christopherwang0129SE/monkey-office/3d Model officemonkey.dk/chat-notes/2026-05-23-sessions.md

# Chat-noter — 2026-05-23

> **Note:** Disse er historiske chat-noter. Fil-referencer nedenfor matcher den oprindelige flade struktur fra 2026-05-23. Repo'et blev omstruktureret samme aften — se [`../README.md`](../README.md) for nuværende lokationer (`product/`, `design/`, `hardware/`).

Noter fra chat-session om visuel design af noise-monkey produktet.

## Spørgsmål fra Gustav

> "Kan du se planning for the office monkey hvordan den skal være? Skal vi prøve at lave et billede af den med nano banana for at backward-engineere?"

## Hvad findes (kortlagt i chatten)

Planning ligger i `agent360-jesperai/agent360/docs/planning/`:

- `2026-05-23-product-plan.md` — koncept låst: 3D-printet desk-abe, hænder-over-mund når dB-tærskel brydes, solgt per-desk/per-zone + dB-dashboard
- `2026-05-23-noise-monkey-research.md` — business outcome research (66% produktivitetstab, 86 min/dag, 23 min refokus, etc.)
- `2026-05-23-noise-monkey-killer-usps-deck.md` — USP-deck
- `2026-05-23-noise-monkey-sales-strategy.md` — sales-strategi
- `2026-05-23-competitor-research-and-usp.md` — konkurrent-research

I dette repo (`office-monkey-hackaton`) på chat-tidspunktet (før restrukturering):
- `Mokey-product-plan.md`, `Research.md`, `PRINT.md`, `design-v1.md`, `design-critique.md`
- `cad/`, `stl/`, `prints/`

(Disse filer ligger nu i `hardware/dev-brief.md`, `product/research.md`, `hardware/PRINT.md`, `design/brief.md`, `design/critique.md`.)

## Gap

**Visuel / industriel design-spec eksisterer ikke endnu.** Fase 1 "Product design" i `product-plan.md:21` er stadig uafkrydset. Vi har funktionel beskrivelse, men ingen "sådan skal den se ud"-dokument.

## Beslutning

Brug **nano banana** (Google Gemini 2.5 Flash Image i AI Studio) til at backward-engineere den visuelle identitet:
generer billede først → afled 3D-printbar spec, kulturel-fit-beslutning (åbent spørgsmål i `product-plan.md:54`), og cold-call collateral derfra. Billigere end design-loops.

## Starter-prompt til nano banana

```
A small 3D-printed desk figurine of a stylized monkey, sitting on a modern
office desk next to a laptop and coffee cup. The monkey is in a clear
"hands-over-mouth" pose — both palms pressed firmly over its mouth, eyes
wide, slightly embarrassed expression. Matte finish, single-color resin
(warm off-white), roughly 8-10cm tall. Clean low-poly aesthetic suitable
for a Scandinavian office (think Hay / Muuto desk accessories — not toy,
not childish). A subtle dB-sensor microphone-grille on the chest, almost
hidden. Soft daylight from a window, shallow depth of field, product-shot
style. No text, no logos.
```

## Foreslåede næste skridt

1. Skriv 3-4 prompt-varianter (Scandi / japansk kawaii / brutalist / plush-toy) til A/B i nano banana
2. Lav design-spec doc (`2026-05-23-noise-monkey-design-spec.md`) som placeholder der udfyldes når valgt billede er låst
3. Afklar åbne spørgsmål i `product-plan.md:50-54` — særligt kulturel fit af "hænder-over-mund" gesten (DE/FR/US/JP)

## Status

Ingen kode ændret. Ingen filer skrevet udover denne note. Næste handling = generer billeder med nano banana.

---

# Chat-noter — 2026-05-23 (session 2: business research, USP, sales strategy)

Anden chat-session samme dag. Fokus: forretnings-research, USP-formulering, og sales-strategi for noise-monkey produktet.

## Hvad denne session producerede (4 docs, nu i dette repo)

1. **`2026-05-23-product-plan.md`** — Fase 1/2 skelet med låst produkt-definition (3D-printet desk-abe, dækker munden ved dB-tærskel).
2. **`2026-05-23-noise-monkey-research.md`** — 13-sektion dyb business outcome research med ~25 kilder. Fem hovedtal:
   - 66 % produktivitetstab ved én overhørt samtale (Banbury & Berry 2005)
   - 86 min/dag tabt i åbent kontor (Steelcase × IPSOS, 10 500 medarbejdere)
   - 23 min 15 s refokus efter afbrydelse (Gloria Mark, UC Irvine)
   - 35 % tilfredse med kontor-støj (Leesman 2024-25)
   - Distraktion = 93,6 % af årligt produktivitetstab — 15× mere end sygefravær
3. **`2026-05-23-noise-monkey-killer-usps-deck.md`** — 9-slide præsentations-pakke med 5 rangerede USP'er:
   - 🥇 "Shush'en ingen tager personligt" (moaten)
   - 🥈 ROI-tabel: €26-325k/år tabt afhængig af team-størrelse
   - 🥉 ESG-rapport-bevis (WELL v2 + ISO 45003)
   - Zoom-kald-kvalitet
   - Kontorets talisman
4. **`2026-05-23-noise-monkey-sales-strategy.md`** — 12-ugers 0-til-30-betalende-kunder plan. Demo-først strategi: aben sælger sig selv på et bord i 60 sek. Kanaler rangeret (walk-in > cold-call > LinkedIn > Product Hunt). 3-tier pricing (€99/€499/€999) med 30-dages risk-free pilot som universal close.

## Centrale beslutninger der venter (denne uge)

- [ ] Target-segment for uge 3-6 (anbefalet: KBH tech/scale-up 50-200 ansatte)
- [ ] Hardware-leverandør: selv-print vs. Sculpteo/Shapeways for første 30 units
- [ ] Pris-anchor i pitch: €99 vs. €499 (anbefalet: €499 office pack — under godkendelses-grænse)
- [ ] Landing-page placering: agent360.dk/aben vs. separat domæne
- [ ] Benjamins rolle — cold-call ejerskab eller Gustav solo

## Åbne spørgsmål denne session ikke løste

- **Verifikation af de fem hovedtal mod primær-kilder** — research er web-summary-baseret. Skal bekræftes inden kunde-decks. **Benjamins research-task (jf. product-plan.md) er ikke landet i nogen repo endnu** — nul commits fra ham per 2026-05-23.
- **Navn til aben** — Hush Monkey / Quiet Ape / Shhmpanzee / MonkeyMute. Test mod første 5 kontor-chefer.
- **Kulturel fit af "hænder-over-mund" gesten** i DE/FR/US/JP — overlap med session-1 spørgsmål (visuel design).
- **Hardware BOM** — vi gætter €15-35/unit; ikke verificeret med prototype endnu.

## Hvor vi ER (status ved session-slut)

- ✅ Forretnings-research, USP, sales-strategi: dokumenteret
- ❌ Prototype: nul aber bygget
- ❌ Kunde: nul betalende, nul piloter
- ❌ Landing-page: eksisterer ikke
- ❌ Benjamin: nul input

Det er **dag 0** af 12-ugers planen. Næste konkrete valg:
- **A)** Byg hardware (5 aber, 7 dage) → walk-in mandag uge 2
- **B)** Valider købsvilje med 20 cold-calls FØR vi bygger hardware (anbefalet — sparer €500-1500 hvis pitch er forkert)

## Status

Alle 4 docs committet i `agent360-jesperai/agent360/docs/planning/` (commits 944dc9fb9 → a65d17f52, branch `new-website-branch`). Nu også kopieret til dette repo på `gustav-chat-noter` branch.
