christopherwang0129SE/monkey-office/three-wise-monkeys-website-inspiration.md

# Website Inspiration from the Three Wise Monkeys Story

This concept works best as a symbolic, atmospheric website built around perception, restraint, and moral choice rather than a literal or playful monkey theme. The central proverb is commonly expressed as “see no evil, hear no evil, speak no evil,” and is associated with the three figures Mizaru, Kikazaru, and Iwazaru. Sources also connect the motif to Japanese visual culture, especially the well-known carving at the Tōshōgū Shrine in Nikkō, while noting earlier moral roots linked to Confucian and Buddhist traditions.

## Core Creative Direction

A compelling interpretation is to design the site as a journey through three forms of perception: sight, sound, and speech. Each part of the interface can embody one principle, allowing the story to unfold through transitions, concealment, and controlled revelation rather than direct exposition.

Three strong concept directions emerge from the symbolism:

- **Minimal editorial** — a quiet, refined site with three structured panels or chapters, using typography and white space to suggest contemplation.
- **Immersive symbolic** — a more experimental experience where blur, silence, and redaction gradually resolve into clarity, reflecting moral awareness.
- **Cultural narrative** — a museum-like digital story about the shrine carving, the proverb, and its ethical interpretations across cultures.

## Visual Language

The strongest palette is restrained: bone, charcoal, aged wood, stone, temple red, and one muted teal or moss accent. This aligns with the historical and spiritual framing of the motif better than glossy gradients or bright startup colors.

The art direction can borrow from carved wood, shrine architecture, archival labels, and triptych compositions. A three-part visual system is especially effective because the monkeys are individually tied to seeing, hearing, and speaking, making the number three structurally meaningful rather than decorative.

## Layout Ideas

A homepage can be built around a triptych or three-chamber structure. Instead of presenting three identical feature cards, the design can vary density and scale so each section feels distinct while remaining part of a shared symbolic system.

Suggested structure:

1. **Hero** — a striking line such as “What we refuse shapes what we become,” paired with three abstract marks or masks that respond to cursor movement.
2. **See** — imagery appears partially obscured, then sharpens as the user scrolls, expressing selective vision and moral attention.
3. **Hear** — ambient sound or waveform visuals stay muted until intentionally activated, reinforcing mindful listening.
4. **Speak** — redacted or fragmented text resolves into clear statements, suggesting disciplined speech.
5. **Origins** — an editorial timeline covering the Japanese shrine carving and the broader ethical tradition behind the proverb.
6. **Modern paradox** — a reflective section exploring how the phrase can also imply silence, denial, or complicity when wrongdoing is ignored.

## Interaction Concepts

The site should use interaction as metaphor. Instead of decorative animations, movement should embody withholding, filtering, and disclosure.

Useful motifs include:

- Masked reveals for images and headlines, especially for the “See” section.
- Audio-on-intent interactions rather than autoplay for the “Hear” section.
- Text censorship and restoration effects for the “Speak” section.
- A light/dark mode contrast that shifts the work from reflective spirituality toward moral ambiguity.

## Tone and References

Two interpretive tones are especially strong. The first is philosophical and meditative, presenting the proverb as guidance about ethical discipline. The second is darker and more critical, using the same proverb to explore censorship, avoidance, or the refusal to confront wrongdoing.

Useful moodboard keywords include:

| Direction | Keywords |
|---|---|
| Philosophical | “ethical restraint,” “ritual silence,” “inner discipline” |
| Japanese craft | “wood carving,” “shrine geometry,” “aged lacquer,” “cedar and stone” |
| Editorial | “triptych grid,” “museum label,” “archival minimalism,” “quiet luxury” |
| Critical | “complicity,” “blindness,” “censorship,” “moral ambiguity” |

## Practical Recommendation

The most distinctive version would combine an editorial layout with symbolic interaction. That approach preserves elegance, avoids cliché, and gives the story enough conceptual depth to feel like a designed cultural experience rather than a themed landing page.
