christopherwang0129SE/monkey-office/3d Model officemonkey.dk/product/plan.md

# Product Plan — 2026-05-23

Captured from Gustav's brief on 2026-05-23. This is the raw skeleton; each section below is a placeholder for the actual artifact to be produced. No content has been inferred — only structure.

---

## Product (locked 2026-05-23)

A 3D-printed desk monkey that measures ambient sound (dB) and physically covers its mouth (hands-over-mouth pose) when the noise crosses a configurable threshold. Sold to offices per-desk or per-zone, with an optional dB-logging dashboard for facilities/HR.

## Tasks (artifacts to produce)

- ✅ **Business outcome research facts** — see [research.md](research.md) (research + USP shortlist). Owner: Benjamin to verify primary-source numbers before customer-facing use.
- **Pure product plan** — owner: Gustav

---

## Fase 1 — Plan & sharpen

- [ ] Product planning
- [ ] Product design
- [x] Research USP → turn into a sales weapon — see [killer USPs deck](usps.md)

**Exit criteria for Fase 1:** USP is articulated as a one-line claim a salesperson can lead a cold-call with, and the product spec is concrete enough that build can start in Fase 2 without further design loops.

---

## Fase 2 — Build + go-to-market in parallel

### Product marketing
- [ ] Walk into offices (in-person outreach)
- [ ] Cold call

### Product
- [ ] Put product together
- [ ] 3D printer — put together
- [ ] Add to team — "cold office" hire

**Exit criteria for Fase 2:** A working product is in customers' hands and there is a repeatable outbound motion (office walk-ins + cold calls) generating qualified conversations.

---

## Launch

- [ ] Product Hunt launch — plan the date, asset list, and pre-launch hunter outreach once Fase 2 is delivering

---

## Open questions

- "Add to team — cold office" — is this a hire dedicated to physical office outreach, or someone who works from a cold/cheap office? Clarify role before recruiting.
- LinkedIn outreach was mentioned then dropped — include in Fase 2 marketing, or out of scope?
- Pricing tier to lead with (€99 single / €499-999 office pack / per-seat SaaS)? Decide based on first 10 cold-call signals.
- Cultural / regional fit of the "monkey covers mouth" gesture (DE/FR/US/JP) — confirm before locking figurine.

---

## Status

- Draft v0 — 2026-05-23
- Not yet linked to V0.1 services plan (`v0.1-services-plan.md`) or solo-pivot doc (`2026-05-06-solo-pivot-and-v0.1-services.md`). Decide whether this product is a new V0.1 line item or a separate track.
