christopherwang0129SE/monkey-office/3d Model officemonkey.dk/product/usps.md

# Noise-Monkey — Killer USPs til præsentation

**Formål:** Slide-klare USP'er der gør produktet til en no-brainer for kontor-chef / HR-lead / office manager. Bygget på research i [research.md](research.md).

**Forudsætning:** Køber er ikke teknisk, har wellness-budget, har modtaget støj-klager, og kan godkende €500-1000 uden indkøbsafdeling. Vi sælger ikke et produkt — vi sælger en *beslutning de gerne vil træffe*.

**Pitch-rytme (15 min):** 1 minut "why now" → 5 minutter på USP #1 og #2 (de vinder salget) → 3 minutter på #3-5 (de lukker indvendingerne) → 3 minutter no-brainer-close → 3 minutter Q&A.

---

## SLIDE 1 — Sandheden om dit kontor

> **På et åbent kontor mister hver medarbejder 86 minutter om dagen til støj.**
> Det er ikke en mening. Det er Steelcase × IPSOS på 10 500 medarbejdere.

**Tre tal til slidet:**
- **66 %** produktivitetsfald ved én overhørt samtale i nærheden (Banbury & Berry)
- **23 min 15 s** at fokusere igen efter en afbrydelse (Gloria Mark, UC Irvine)
- **35 %** er tilfredse med støjniveauet på deres kontor (Leesman 2024-25)

**Closing-linje:** *"Du har enten allerede mistet pengene — eller du betaler dem hver dag uden at vide det."*

**Visuel:** En kontor-tegning. Tre rectangles der lyser rødt med tallene. Aben sidder i hjørnet med hænderne for munden, lille og diskret. Ingen logo endnu.

---

## SLIDE 2 — 🥇 USP #1: "Shush'en ingen tager personligt"

> **Aben siger til. Dine medarbejdere gør ikke.**

**Body (slide-tekst):**
Det dyreste problem på et åbent kontor er ikke støjen. Det er at **ingen vil bede en kollega være stille**. Det er socialt giftigt — derfor vokser støjen indtil de produktive medarbejdere arbejder hjemmefra eller siger op.

Aben løser det ved at flytte håndhævelsen væk fra mennesker. Den er datadrevet (dB-grænse), neutral, og endda sjov. Ingen tager det personligt at en abe holder sig for munden.

**Killer-fact:**
> **99 % af medarbejdere siger kontor-støj forringer deres koncentration. 0 % vil sige det til en kollega.** (Steelcase + sund fornuft.)

**Hvorfor denne USP er moaten:**
- Apps måler. → ændrer ikke adfærd.
- Akustik-paneler absorberer. → ændrer ikke adfærd.
- Sound-masking pumper rosa støj ud. → skjuler problemet, ændrer ikke adfærd.
- Lyd-bokse isolerer. → flytter en person ad gangen.
- **Aben er det eneste der ændrer adfærden hos kilden i real-time uden at et menneske skal være "den dårlige fyr".**

**Closing-linje:** *"Du sælger ikke en sensor. Du sælger fred i kontoret."*

**Visuel:** Foto/render af to medarbejdere der griner og dæmper sig selv, mens aben i forgrunden lige har dækket munden. Tekst-overlay: "Den siger til. Du behøver ikke."

---

## SLIDE 3 — 🥈 USP #2: "86 minutter om dagen pr. medarbejder = €1 200-6 500 pr. år"

> **Med 40 ansatte mister du ~€50 000-260 000 om året til støj. Aben koster en brøkdel.**

**ROI-tabel (skal stå på slidet):**

| Medarbejdere | Konservativ recapture (2 %) | Realistisk (5 %) |
| --- | --- | --- |
| 20 | **€26 000/år** | **€65 000/år** |
| 40 | **€52 000/år** | **€130 000/år** |
| 100 | **€130 000/år** | **€325 000/år** |

(Baseret på €69/time loaded cost, 1 880 arbejdstimer/år, jf. Glassdoor + standard 1,3x benefit-multiplier.)

**Killer-fact:**
> **Distraktion var 93,6 % af det årlige produktivitetstab hos én stor amerikansk arbejdsgiver — 15 gange dyrere end sygefravær.** Du har allerede et 7-cifret problem. Du ved bare ikke det.

**Sammenligning (skal vises som søjlediagram):**
- Awair (luftkvalitets-monitor) påstår **$6 500-15 500/medarbejder/år** i produktivitetsgevinst.
- Støj er den **#1 medarbejder-klage** om kontoret. Større end luft.
- Vores påstand er **mere konservativ** end Awairs, og luften har de allerede købt.

**Closing-linje:** *"Hvis aben bare reducerer dit produktivitetstab med 1 %, har den betalt sig hjem i uge 2."*

**Visuel:** Søjlediagram der viser kontorets støj-tab i én stor rød søjle vs. abens pris i en tynd grøn streg. Tilbagebetalings-vinduet markeret i kalender-grafik: "Uge 1 — installation. Uge 2 — break-even. Uge 3+ — ren gevinst."

---

## SLIDE 4 — 🥉 USP #3: "Din ESG-rapport lover wellbeing. Hvor er dB-loggen?"

> **Du kan ikke rapportere på en metric du ikke måler. Vi giver dig metric'en og audit-trail'en.**

**Body:**
WELL Building Standard v2 kræver max NC 40 i åbne kontorer, NC 35 i lukkede. **ISO 45003 (2021)** — den globale standard for psykisk arbejdsmiljø — definerer **støj som en anerkendt psykosocial fare**. Tilsynsmyndigheder i UK, EU og Nordamerika skifter fra at tjekke politikker til at kræve **dokumentation af systematisk håndtering**.

Dit ESG-bilag og din arbejdsmiljø-rapport siger "vi beskytter medarbejdernes trivsel". Aben er det eneste produkt på markedet der **leverer beviset løbende**.

**Killer-fact:**
> **Når en arbejdsmiljø-tilsyn spørger hvordan I håndterer psykisk arbejdsmiljø, har du så data — eller har du en mening?**

**Hvem dette overbeviser:**
- HR / People & Culture (de skal levere ESG-S tallene)
- Legal (de vil have audit-trail)
- CSR / Sustainability lead (de mangler S-pillar-metrics)
- Bestyrelses-medlem der har ESG på agendaen

**Closing-linje:** *"Det her er ikke en gadget. Det er en compliance-artefakt der ligner en abe."*

**Visuel:** Dashboard-screenshot der viser dB-graf over tid, med thresholds markeret. Side om side med uddrag af WELL v2 / ISO 45003-tekst der nævner støj. Tekst-overlay: "Politik → bevis."

---

## SLIDE 5 — USP #4: "Bedre Zoom-opkald uden at flytte en væg"

> **Hver eneste call leaker dit kontor til kunder. Microsoft og Zoom byggede AI for at fjerne støjen i skyen. Vi fjerner den ved kilden.**

**Body:**
I 2026 er kontoret en **lyd-arena**. Møder er kamera-på, mikrofon-på, hele dagen. Microsoft Teams har shippet **tre niveauer af AI-baseret støj-reduktion** specifikt fordi den underliggende støj er universel — og det fortæller dig at problemet er for stort til at fixe i skyen.

Aben fixer det 1 meter fra mikrofonen, før Teams overhovedet skal arbejde.

**Killer-fact:**
> **Microsoft byggede AI for at skjule din baggrunds-støj. Det er en milliard-dollar tilståelse af at problemet er ufixbart fra cloud'en.**

**Hvem dette overbeviser:**
- Salgs-chefen (reps er i telefonen hele dagen — kunder hører kontoret)
- Customer Success / Support leads (kald-kvalitet = NPS)
- Konsulent-huse, advokat-firmaer, revisorer (klient-fortrolighed)

**Closing-linje:** *"Din næste kunde hører dit kontor før de hører dit pitch. Hvad skal kontoret lyde som?"*

**Visuel:** Split-screen. Venstre: forretningsperson på Zoom med larm bag sig + tekst-overlay "før". Højre: samme person, stille, med aben på bordet bag sig + "efter". Bunden: Microsoft Teams logo + "ships 3-level AI noise suppression — fordi problemet er for stort til kun at løse i softwaren."

---

## SLIDE 6 — USP #5: "Kontorets talisman"

> **Planter, ergo-stole, stå-borde. Alle dine wellness-investeringer er usynlige for kandidater og besøgende. Aben er det første de ser.**

**Body:**
Gen Z og millennials prioriterer trivsel højere end nogen tidligere generation. Glassdoor-anmeldelser nævner ofte "kunne ikke koncentrere mig" og "skulle altid have headphones på" som grund til 1-stjerne.

Aben er **fotografisk, postbar, og signalerer instant** at det her er et sted der tager arbejdsmiljø seriøst. En LinkedIn-post med aben der dækker munden under en travl eftermiddag slår 99 % af employer-brand indhold.

**Killer-fact:**
> **Du har allerede betalt for planter og stå-borde. Ingen ser dem på Glassdoor. Aben er den eneste wellness-investering der er sin egen markedsføring.**

**Hvem dette overbeviser:**
- CHRO / Talent Acquisition
- Founder-CEO i scale-up med kultur-fokus
- Office manager der vil have noget der bliver bemærket
- Marketing-chef der mangler authentic content

**Closing-linje:** *"Hver gang den dækker munden, fortjener I et nyt LinkedIn-billede."*

**Visuel:** En grid af 6 sociale media-stills: aben på et hot-desk, aben med teamet om sig, aben på et investor-besøg, aben i et nyt-ansat-velkomstbillede. Tekst-overlay: "Wellness-investeringer du faktisk kan vise frem."

---

## SLIDE 7 — Hvorfor det her er en no-brainer

**Fire grunde, ét slide:**

### 1. Prisen er under din godkendelses-grænse
Office starter-pack: ~€499-999. Ingen indkøb, ingen approval-chain, ingen forsinkelse. Din wellness-konto kan absorbere det i dag.

### 2. Risk-free trial
Vi sender X aber. Hvis kontoret ikke er mærkbart roligere på 30 dage, betaler du intet. Du har **ingen downside**.

### 3. Det passer i wellness-budgettet du allerede har
Danske firmaer >1000 medarbejdere bruger **$2 400/medarbejder/år** på wellness. Små firmaer ~$720/år. Aben er <1 % af det budget pr. medarbejder — og er den eneste investering du kan måle løbende.

### 4. Du er helten
Det her er **din** beslutning. Aben er synlig. Medarbejdere takker dig. Glassdoor bemærker det. Det er et "did something visible" check i din kvartals-review.

**Closing-linje:** *"Du behøver ikke godkendelse. Du behøver ikke en business case. Du behøver én abe og 30 dage. Hvis du tager fejl, sender du den tilbage."*

---

## SLIDE 8 — Indvendinger & svar

| Indvending | Svar (én linje, læg vægt) |
| --- | --- |
| *"Vi har headphones."* | "Headphones isolerer den der lider. Aben adresserer den der støjer. Du behandler symptom vs. kilde." |
| *"Det er bare en gadget."* | "For medarbejderen er det en gadget. For dig er det et dashboard, et ESG-bilag og en stille office manager-talsmand." |
| *"Det er for dyrt."* | "Det er billigere end at miste én medarbejder. Replacement-cost er 150 % af løn — i jeres tilfælde {beregn}. Aben skal kun forhindre én exit pr. årti for at betale sig hjem." |
| *"Folk vil føle sig overvågede."* | "Den måler dB. Den kender ikke ord. Ingen mikrofon-data forlader enheden. Sammenlign med kameraet i jeres reception." |
| *"Vi har ikke det problem."* | "60 % af kontorer afbrydes af støj mindst 2x/uge. 35 % er tilfredse. Statistisk har I problemet — I har bare normaliseret det." |
| *"Lad os vente til Q4-budget."* | "Hver uge i venter koster jer ~{beregn på 86 min × medarbejdere × €1,15/min} i tabt produktivitet. Beslutningen er ikke om I køber. Den er om I venter med at stoppe blødningen." |
| *"Vi skal lige tale med vores akustiker."* | "Glimrende. Akustik-paneler dæmper alt. Aben targets specifikt den menneskelige støj — adfærd, ikke fysik. De er komplementære, ikke konkurrerende." |

---

## SLIDE 9 — The Close

**Et spørgsmål:**
> "Vil du gerne være den person der løste dette her i denne kvartal — eller den der vidste det og ventede?"

**Et tilbud:**
> "5 aber på dit kontor i 30 dage. Hvis støj-klagerne ikke falder, sender du dem tilbage og betaler nul. Hvis de falder — og det gør de — så fortsætter vi samtalen om rest-licensen."

**Et action-item:**
> "Skal jeg sende dig en pilot-aftale i aften, så I kan starte mandag?"

---

## Bilag — Hvordan denne deck'en bruges

**Til kolde opkald (DKK 30 sek):**
> "Hej, jeg har et produkt der reducerer kontor-støj uden at jeres medarbejdere skal shush'e hinanden. Steelcase siger I taber 86 min/dag/person til støj. Jeg har en abe der løser det. Har du 15 minutter til en demo?"

**Til office-walk-ins:**
- Tag 1-2 aber med
- Stil den på modtagelse-disken under samtalen
- Lad den naturligt dække munden (juster threshold under demo) — dét er pitchen
- Del kontaktet til dig som "den der løser noget vi ikke kan løse selv"

**Til LinkedIn outreach:**
- Headline-hook: USP #1 ("Shush'en ingen tager personligt")
- Body: USP #2 ROI-tabellen
- CTA: USP #7 risk-free-trial

**Til Product Hunt launch:**
- Hero-visuel: aben der dækker munden i et åbent kontor (video, ikke billede)
- Headline: "The noise meter that closes its own mouth"
- Tagline: "Built for the open-plan offices that everyone hates but nobody fixes"
- Lead-USP: #1 og #5 (de er de mest viral-egnede — #2-3 er for B2B-tunge til PH-publikum)

---

**Status:** Draft v1 — 2026-05-23. Bygget direkte på research-doc'en. **Test mod 5 kolde opkald før vi laver det til Keynote-slides** — sproget skal slibes på rigtige kontor-chefer, ikke teoretiseres alene.
