christopherwang0129SE/monkey-office/3d Model officemonkey.dk/stl/_triggered.png

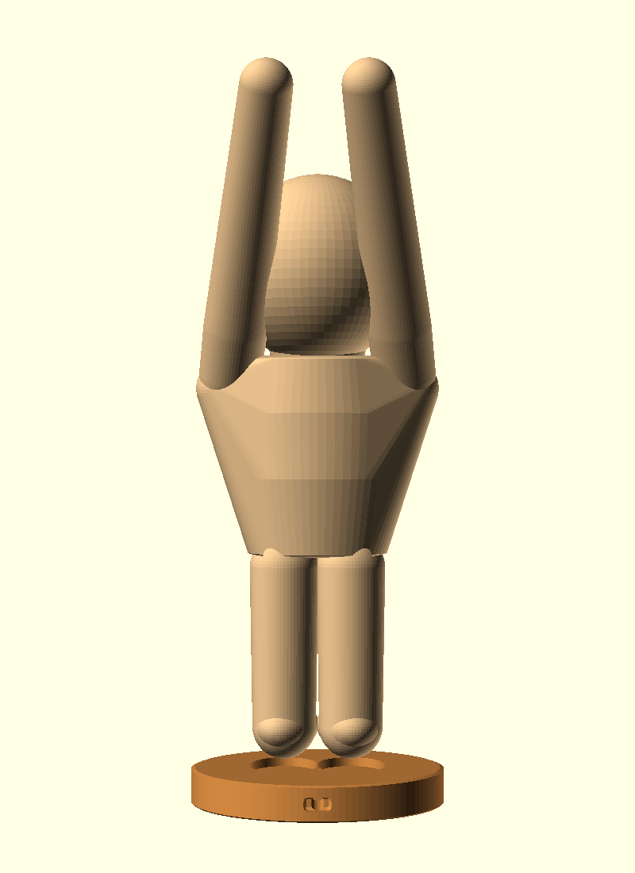
3d Model officemonkey.dk/stl/_triggered.png
