christopherwang0129SE/monkey-office/3d Model officemonkey.dk/stl/wall/_back.png

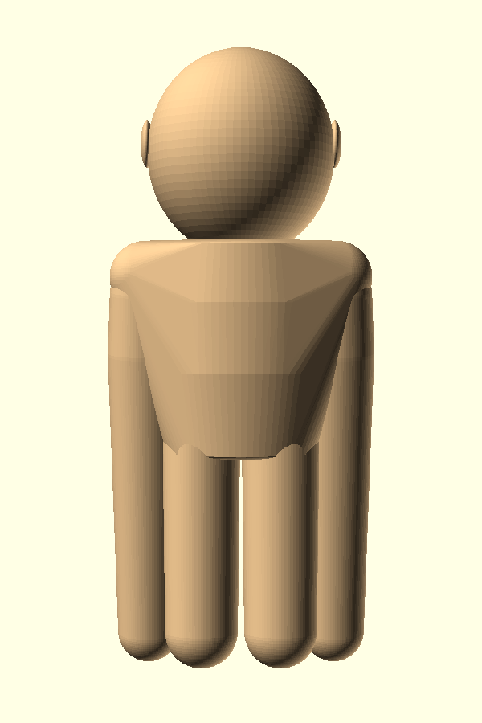
3d Model officemonkey.dk/stl/wall/_back.png
