christopherwang0129SE/monkey-office/3d Model officemonkey.dk/stl/wall/_iso.png

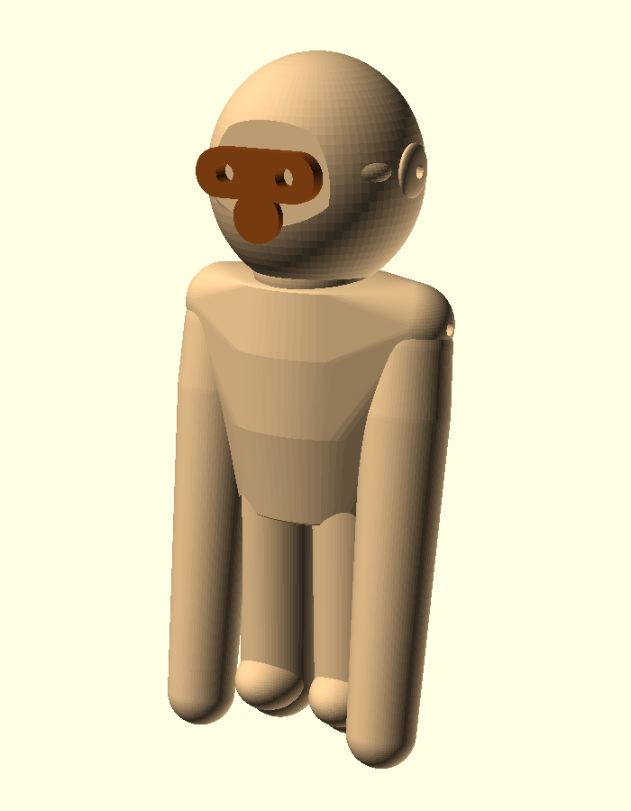
3d Model officemonkey.dk/stl/wall/_iso.png
