christopherwang0129SE/monkey-office/3d Model officemonkey.dk/stl/wall/_wall_mockup.png

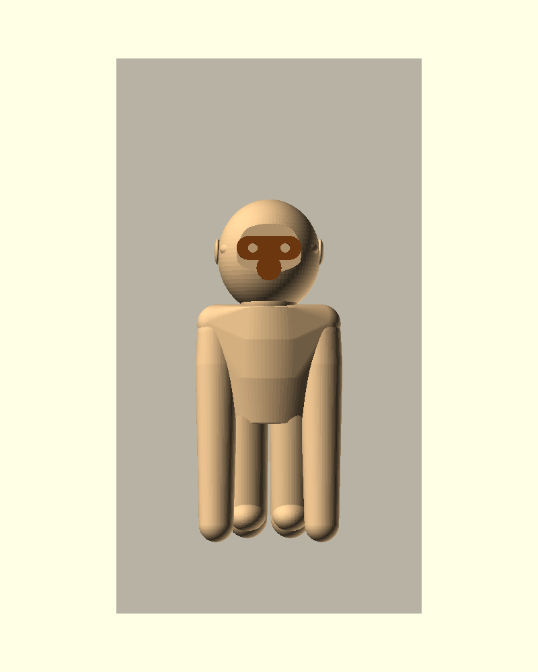
3d Model officemonkey.dk/stl/wall/_wall_mockup.png
