christopherwang0129SE/monkey-office/Tys-aben-Print-Package/individual-parts/desktop/arm_left.stl

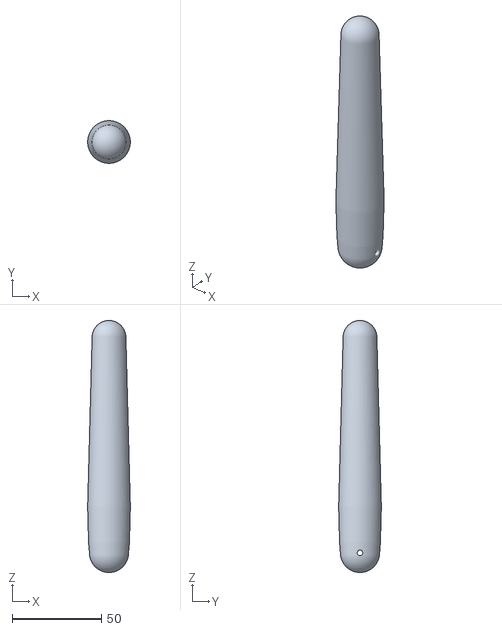
[picture p27: CAD file, 2026-05-23]
Tys-aben-Print-Package/individual-parts/desktop/arm_left.stl
24.0 x 24.0 x 141.5
