christopherwang0129SE/monkey-office/Tys-aben-Print-Package/individual-parts/wall/yoke.stl

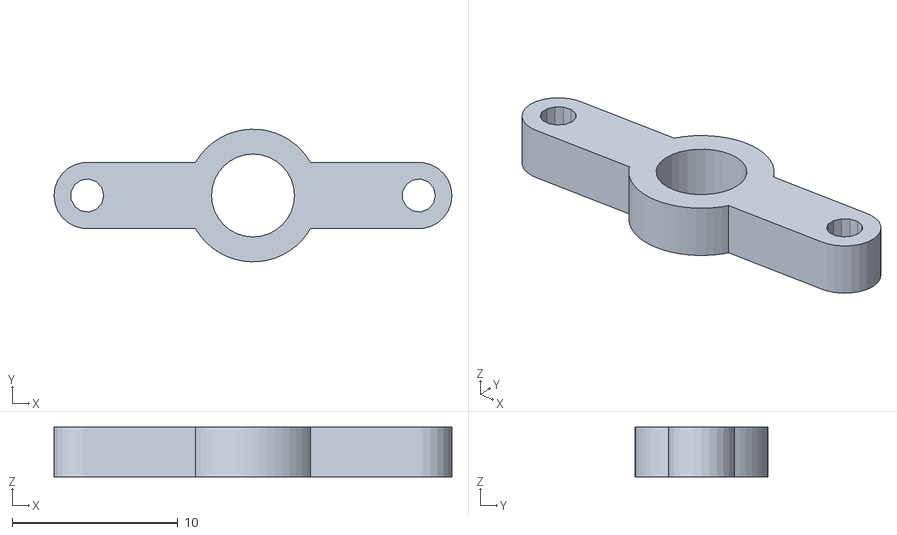
[picture p28: CAD file, 2026-05-23]
Tys-aben-Print-Package/individual-parts/wall/yoke.stl
24.0 x 8.00 x 3.00
