christopherwang0129SE/monkey-office/Tys-aben-Print-Package/individual-parts/desktop/torso_front.stl

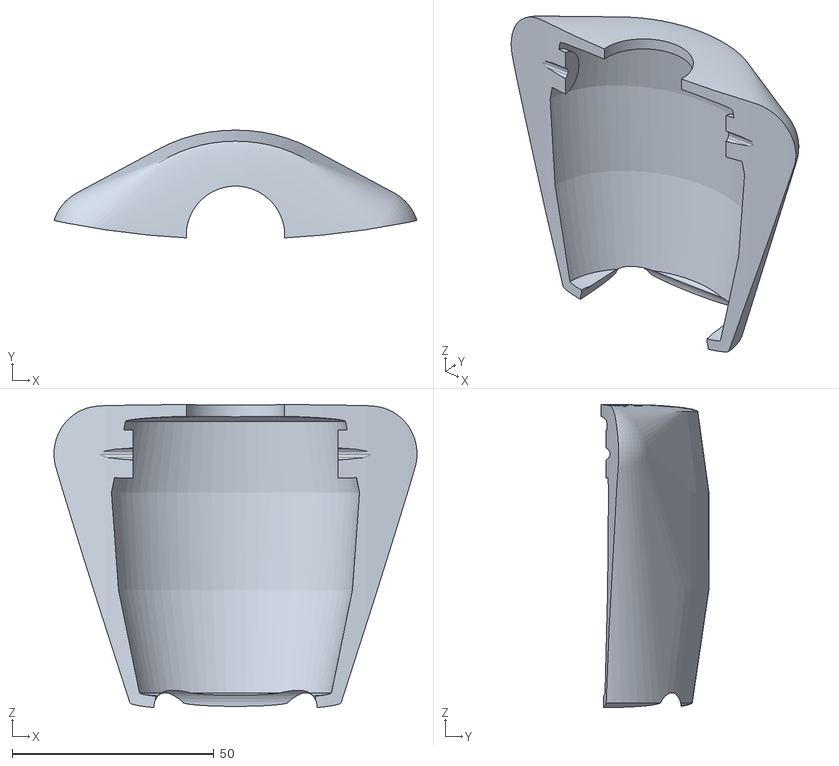
[picture p29: CAD file, 2026-05-23]
Tys-aben-Print-Package/individual-parts/desktop/torso_front.stl
90.0 x 26.7 x 75.2
