christopherwang0129SE/monkey-office/Tys-aben-Print-Package/individual-parts/wall/upper_arm_left.stl

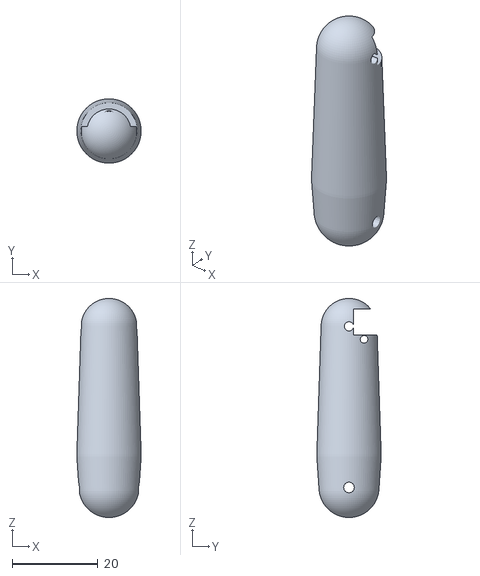
[picture p30: CAD file, 2026-05-23]
Tys-aben-Print-Package/individual-parts/wall/upper_arm_left.stl
15.0 x 15.0 x 51.0
