christopherwang0129SE/monkey-office/Tys-aben-Print-Package/individual-parts/desktop/head.stl

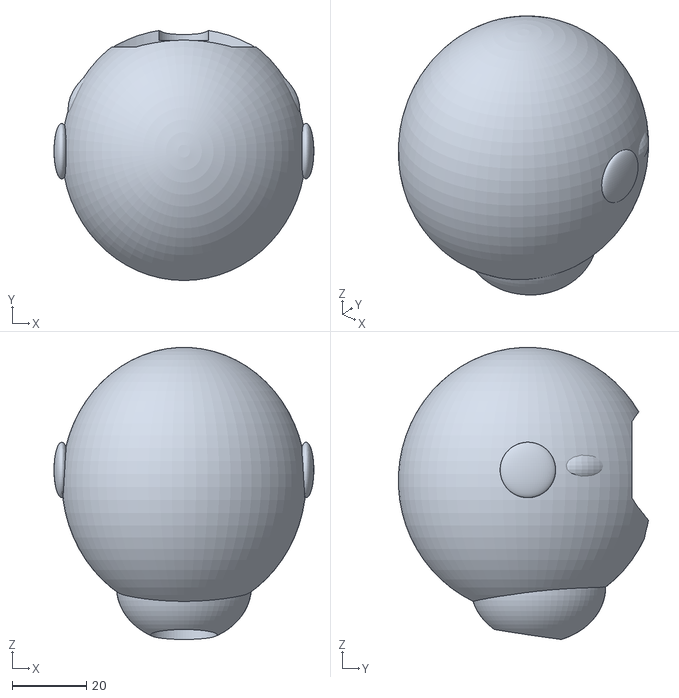
[picture p31: CAD file, 2026-05-23]
Tys-aben-Print-Package/individual-parts/desktop/head.stl
70.2 x 67.5 x 78.9
