christopherwang0129SE/monkey-office/Tys-aben-Print-Package/individual-parts/wall/bottom_plate.stl

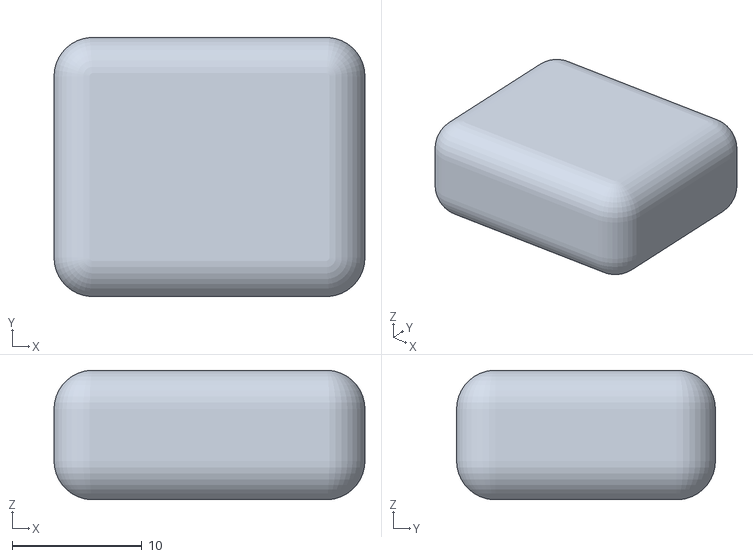
[picture p32: CAD file, 2026-05-23]
Tys-aben-Print-Package/individual-parts/wall/bottom_plate.stl
24.0 x 20.0 x 9.98
