christopherwang0129SE/monkey-office/Tys-aben-Print-Package/individual-parts/wall/eye_board.stl

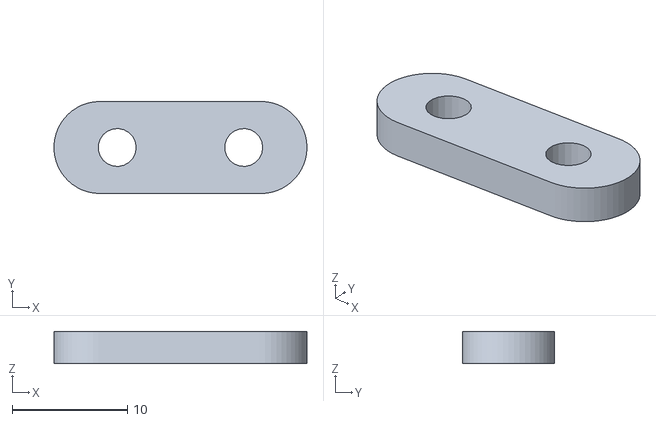
[picture p33: CAD file, 2026-05-23]
Tys-aben-Print-Package/individual-parts/wall/eye_board.stl
22.0 x 8.00 x 2.80
