christopherwang0129SE/monkey-office/Tys-aben-Print-Package/individual-parts/desktop/leg_right.stl

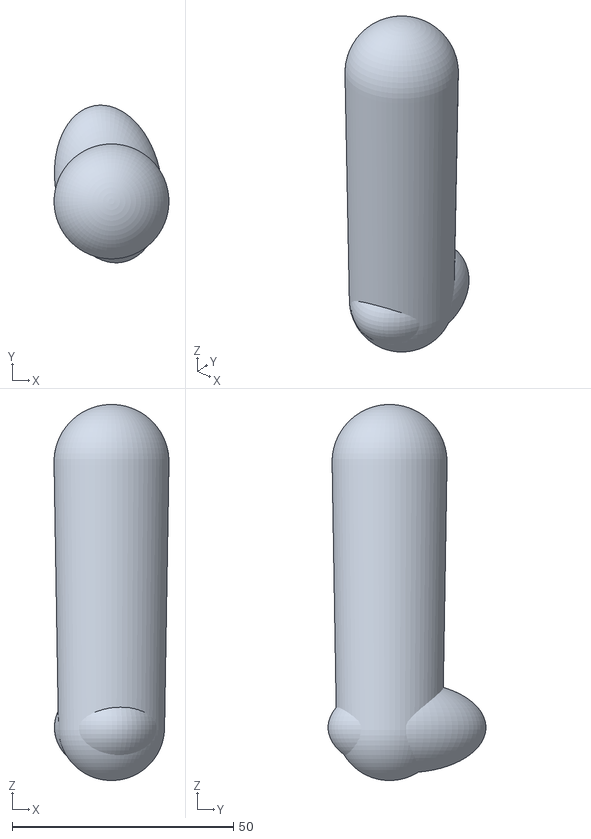
[picture p34: CAD file, 2026-05-23]
Tys-aben-Print-Package/individual-parts/desktop/leg_right.stl
26.0 x 35.6 x 85.0
