christopherwang0129SE/monkey-office/Tys-aben-Print-Package/individual-parts/wall/leg_right.stl

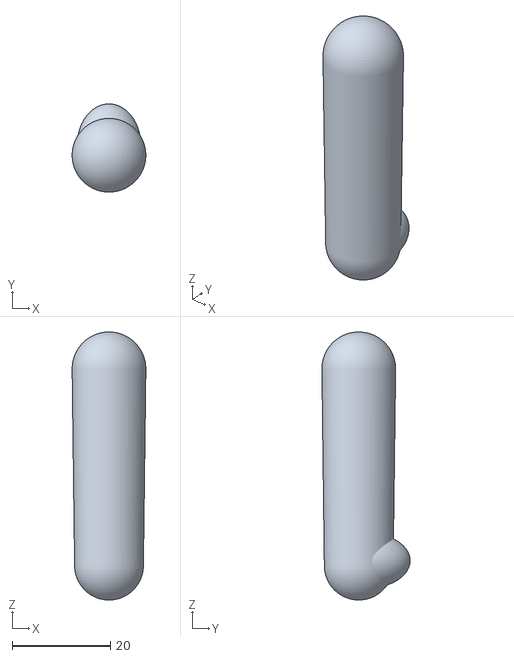
[picture p35: CAD file, 2026-05-23]
Tys-aben-Print-Package/individual-parts/wall/leg_right.stl
15.0 x 17.9 x 54.5
