christopherwang0129SE/monkey-office/Tys-aben-Print-Package/individual-parts/desktop/bottom_plate.stl

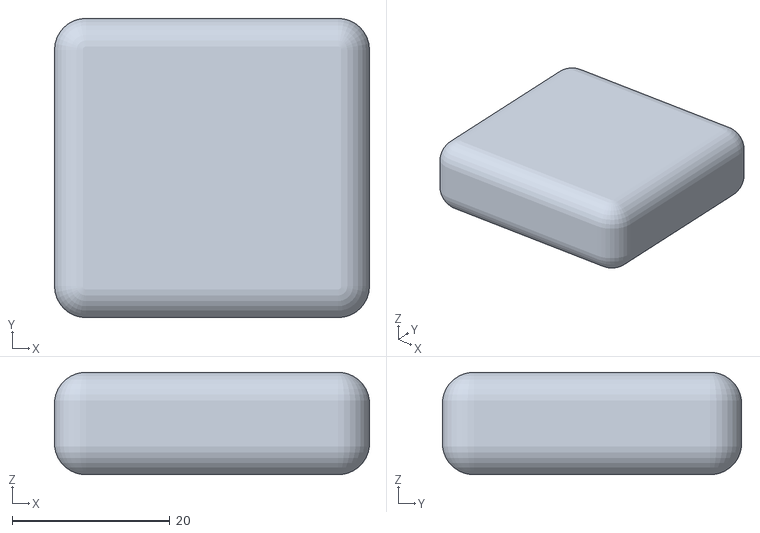
[picture p36: CAD file, 2026-05-23]
Tys-aben-Print-Package/individual-parts/desktop/bottom_plate.stl
40.0 x 38.0 x 13.0
