christopherwang0129SE/monkey-office/Tys-aben-Print-Package/individual-parts/wall/hub_box.stl

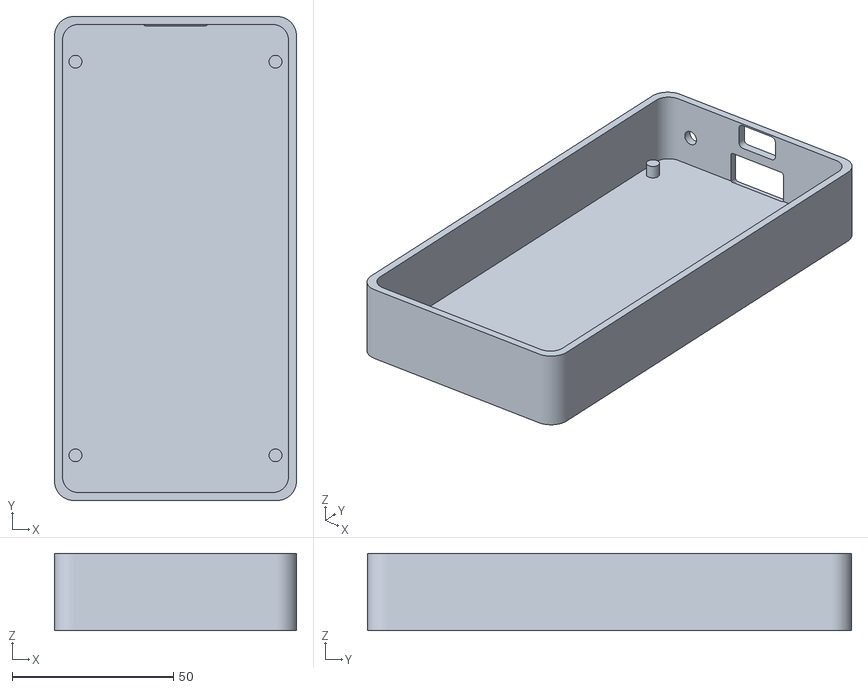
[picture p37: CAD file, 2026-05-23]
Tys-aben-Print-Package/individual-parts/wall/hub_box.stl
75.0 x 150.0 x 24.0
