christopherwang0129SE/monkey-office/Tys-aben-Print-Package/individual-parts/wall/forearm_right.stl

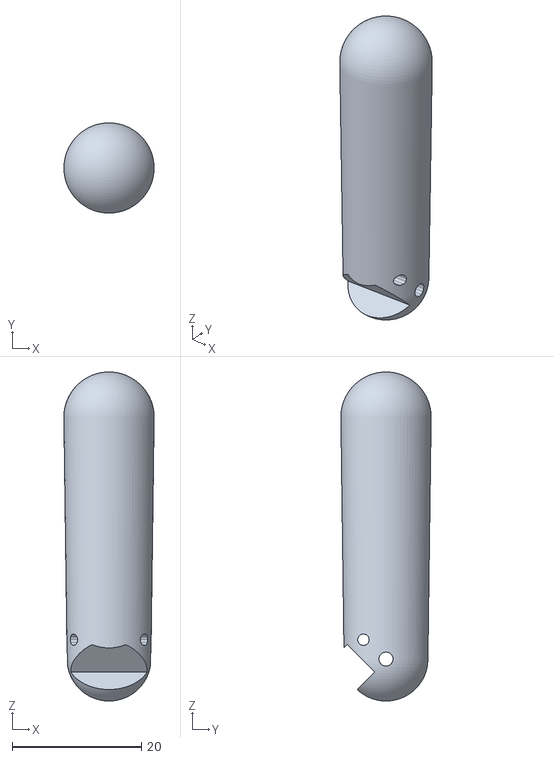
[picture p38: CAD file, 2026-05-23]
Tys-aben-Print-Package/individual-parts/wall/forearm_right.stl
14.0 x 14.0 x 51.0
