christopherwang0129SE/monkey-office/Tys-aben-Print-Package/individual-parts/desktop/muzzle.stl

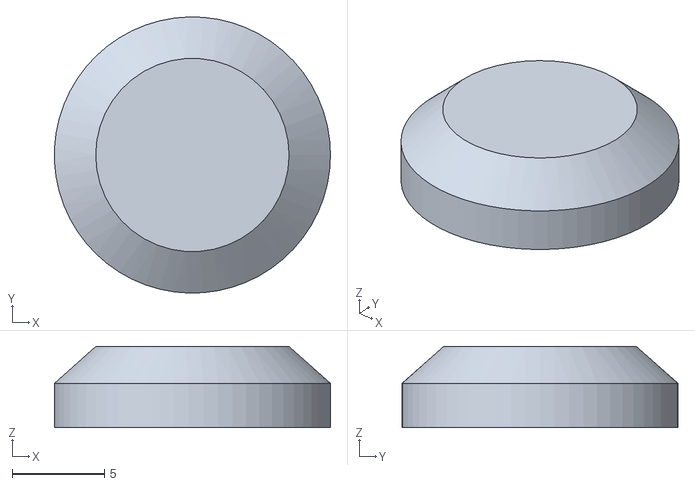
[picture p39: CAD file, 2026-05-23]
Tys-aben-Print-Package/individual-parts/desktop/muzzle.stl
15.0 x 15.0 x 4.40
