christopherwang0129SE/monkey-office/Tys-aben-Print-Package/individual-parts/wall/muzzle.stl

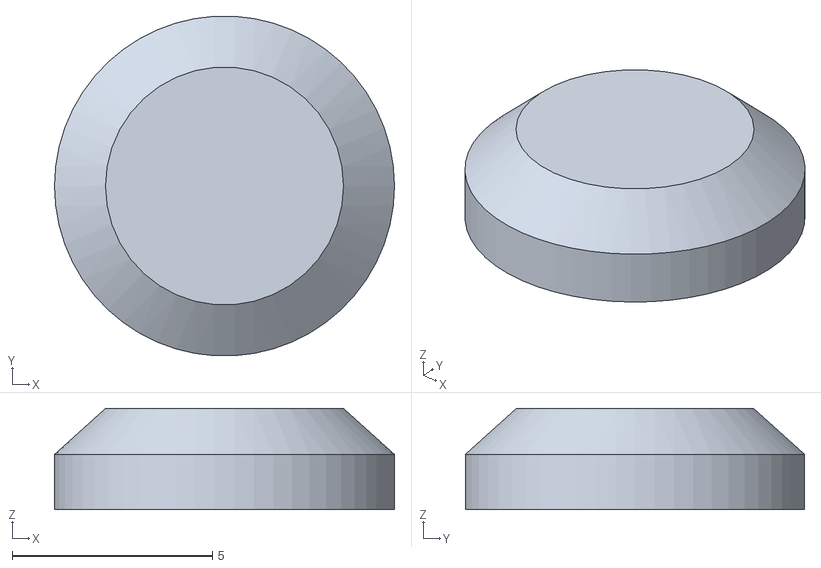
[picture p40: CAD file, 2026-05-23]
Tys-aben-Print-Package/individual-parts/wall/muzzle.stl
8.50 x 8.49 x 2.53
