christopherwang0129SE/monkey-office/Tys-aben-Print-Package/individual-parts/desktop/yoke.stl

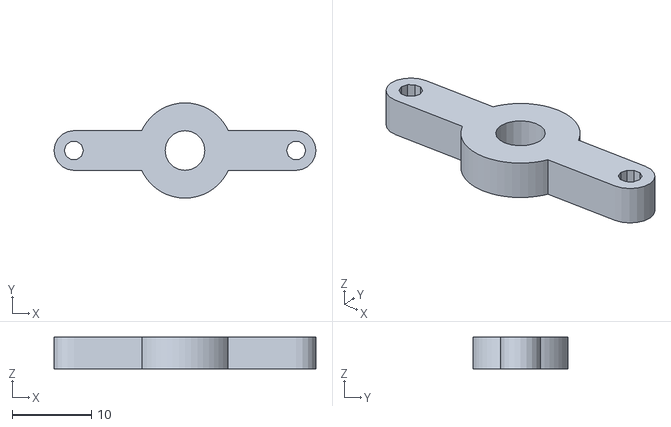
[picture p41: CAD file, 2026-05-23]
Tys-aben-Print-Package/individual-parts/desktop/yoke.stl
33.0 x 12.0 x 4.00
