christopherwang0129SE/monkey-office/Tys-aben-Print-Package/individual-parts/desktop/eye_board.stl

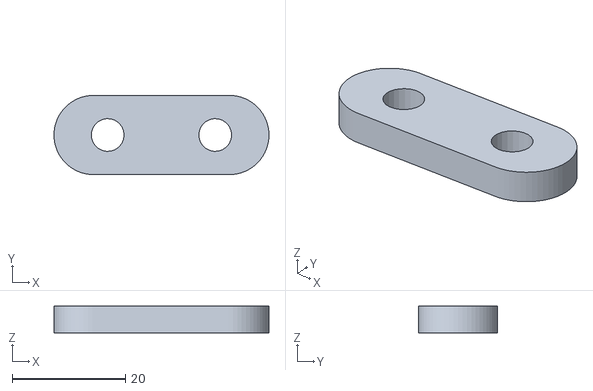
[picture p42: CAD file, 2026-05-23]
Tys-aben-Print-Package/individual-parts/desktop/eye_board.stl
38.0 x 14.0 x 4.70
