christopherwang0129SE/monkey-office/Tys-aben-Print-Package/individual-parts/wall/mic_bracket.stl

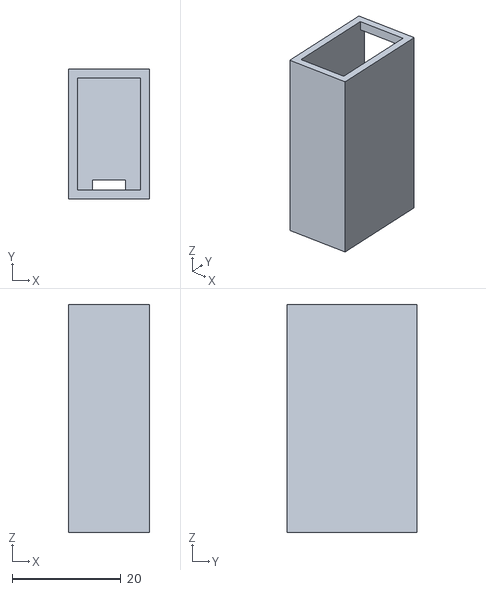
[picture p43: CAD file, 2026-05-23]
Tys-aben-Print-Package/individual-parts/wall/mic_bracket.stl
15.0 x 24.0 x 42.0
