christopherwang0129SE/monkey-office/Tys-aben-Print-Package/individual-parts/desktop/servo_bracket.stl

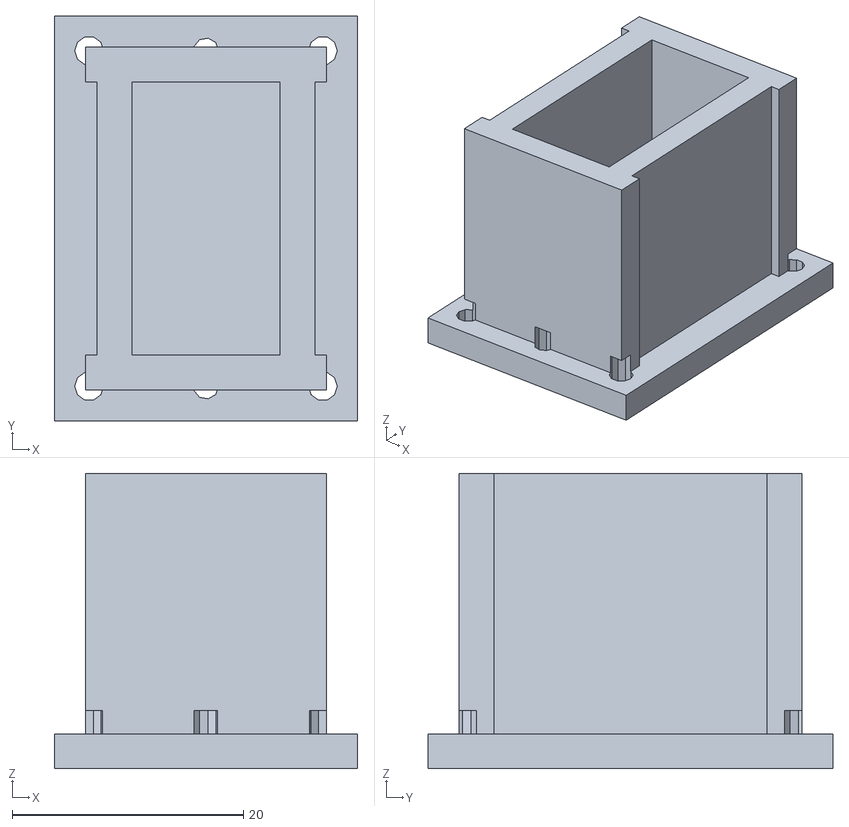
[picture p44: CAD file, 2026-05-23]
Tys-aben-Print-Package/individual-parts/desktop/servo_bracket.stl
26.2 x 35.0 x 25.5
