christopherwang0129SE/monkey-office/Tys-aben-Print-Package/individual-parts/wall/torso_back.stl

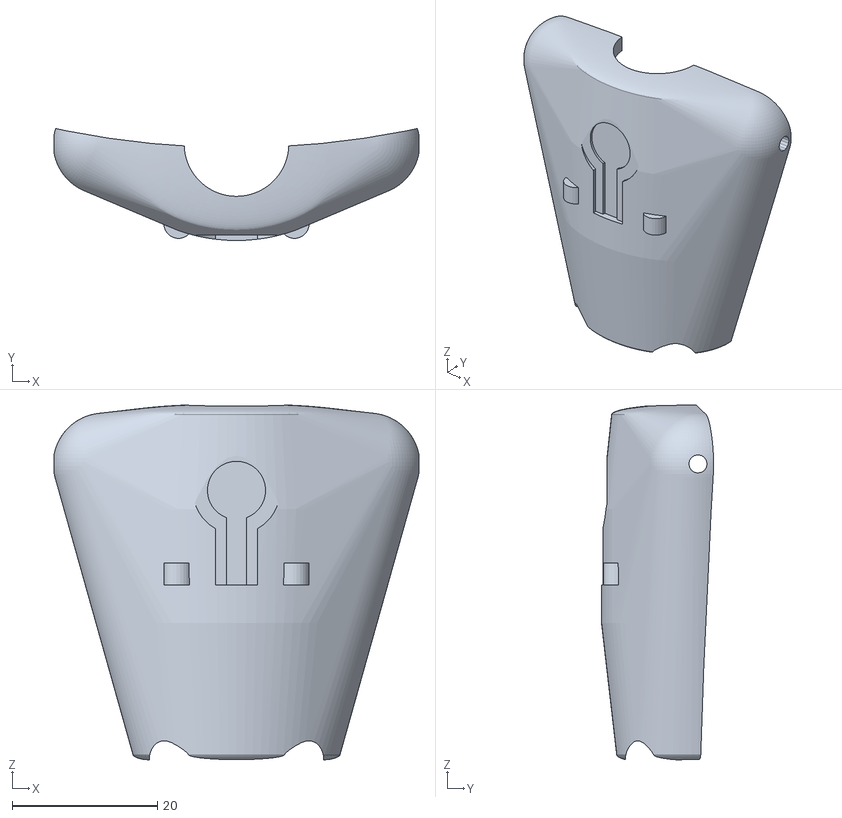
[picture p45: CAD file, 2026-05-23]
Tys-aben-Print-Package/individual-parts/wall/torso_back.stl
50.3 x 15.4 x 48.9
