christopherwang0129SE/monkey-office/Tys-aben-Print-Package/individual-parts/wall/servo_bracket.stl

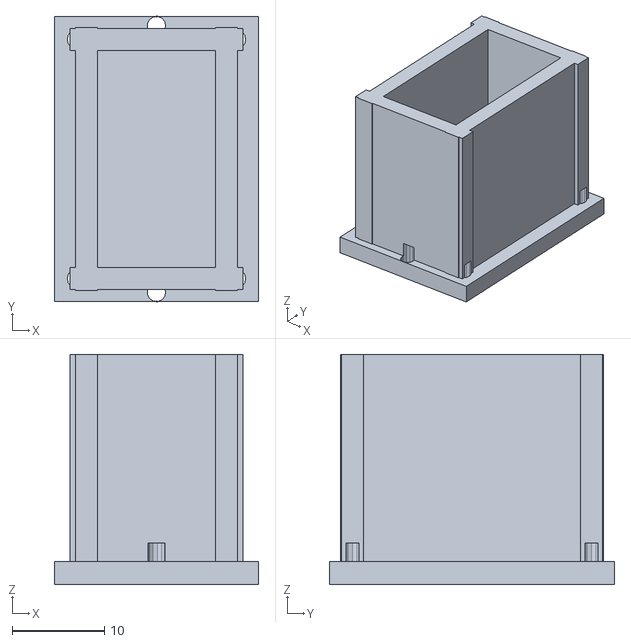
[picture p46: CAD file, 2026-05-23]
Tys-aben-Print-Package/individual-parts/wall/servo_bracket.stl
22.2 x 31.0 x 25.0
