christopherwang0129SE/monkey-office/3d Model officemonkey.dk/prints/plate_1_preview.png

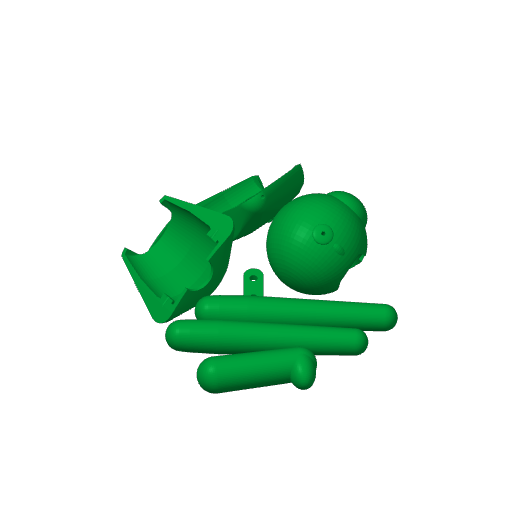
3d Model officemonkey.dk/prints/plate_1_preview.png
