christopherwang0129SE/monkey-office/3d Model officemonkey.dk/prints/plate_2_preview.png

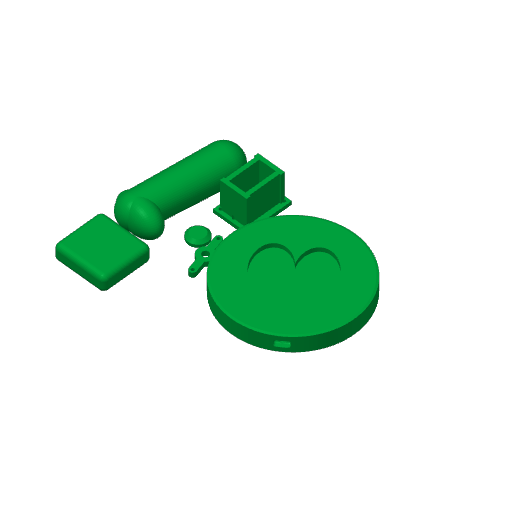
3d Model officemonkey.dk/prints/plate_2_preview.png
