christopherwang0129SE/monkey-office/3d Model officemonkey.dk/prints/wall_plate_preview.png

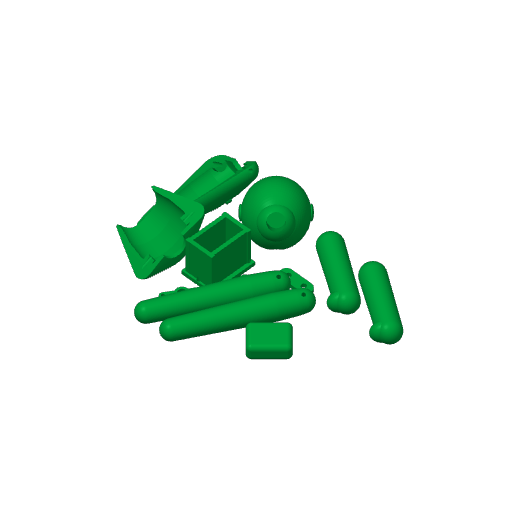
3d Model officemonkey.dk/prints/wall_plate_preview.png
