christopherwang0129SE/monkey-office/3d Model officemonkey.dk/stl/_assembly_front.png

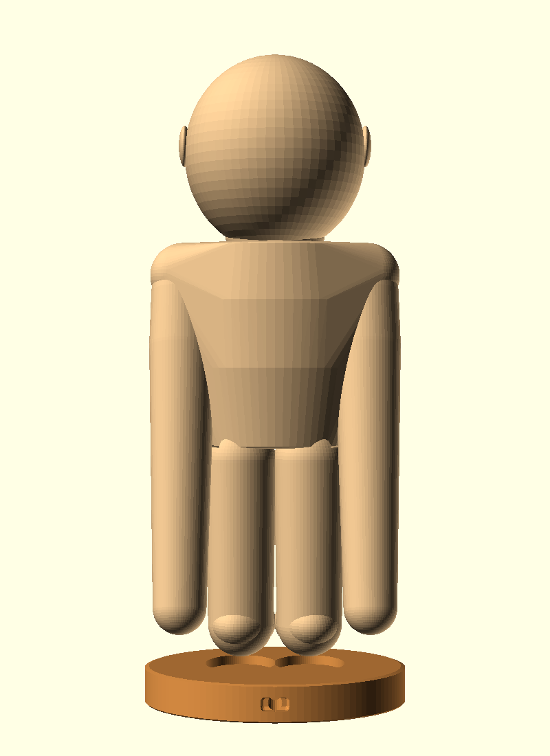
3d Model officemonkey.dk/stl/_assembly_front.png
