christopherwang0129SE/monkey-office/3d Model officemonkey.dk/stl/_assembly_iso.png

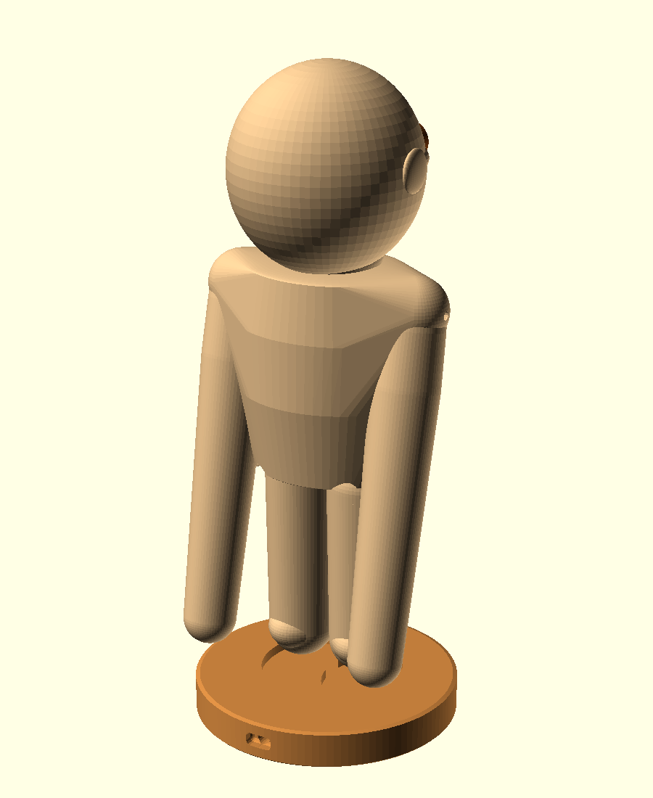
3d Model officemonkey.dk/stl/_assembly_iso.png
