christopherwang0129SE/monkey-office/3d Model officemonkey.dk/stl/_assembly_side.png

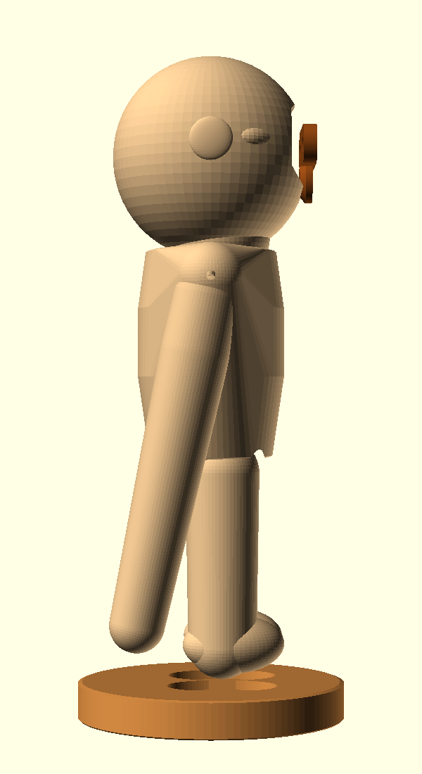
3d Model officemonkey.dk/stl/_assembly_side.png
