christopherwang0129SE/monkey-office/Tys-aben-Print-Package/reference/peak-pose.png

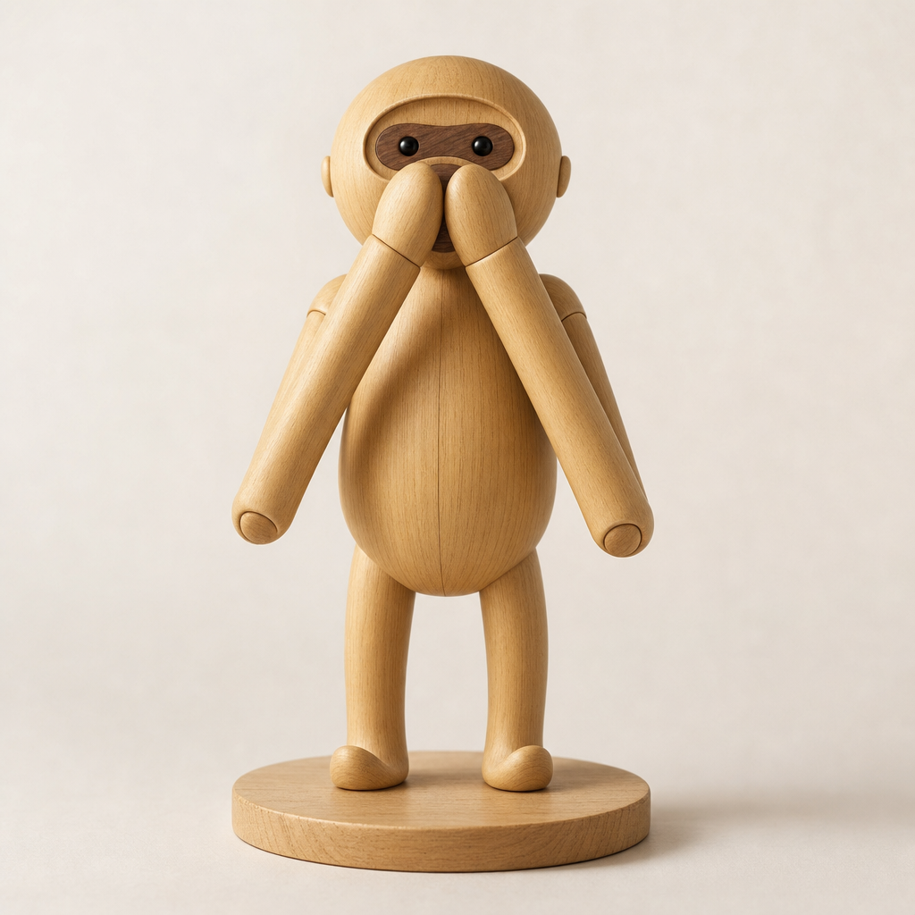
Tys-aben-Print-Package/reference/peak-pose.png
